tsbischof/kunst-und-krebs/doc/box/PXL_20230809_095317557.MP.jpg

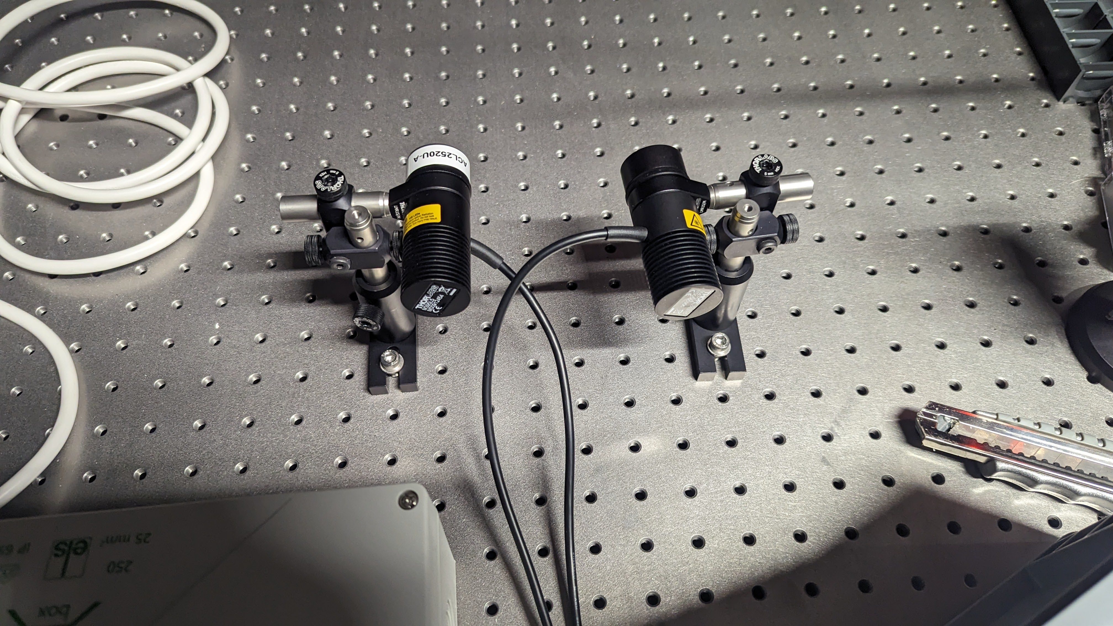
doc/box/PXL_20230809_095317557.MP.jpg
