tsbischof/kunst-und-krebs/doc/box/PXL_20230809_095553471.MP.jpg

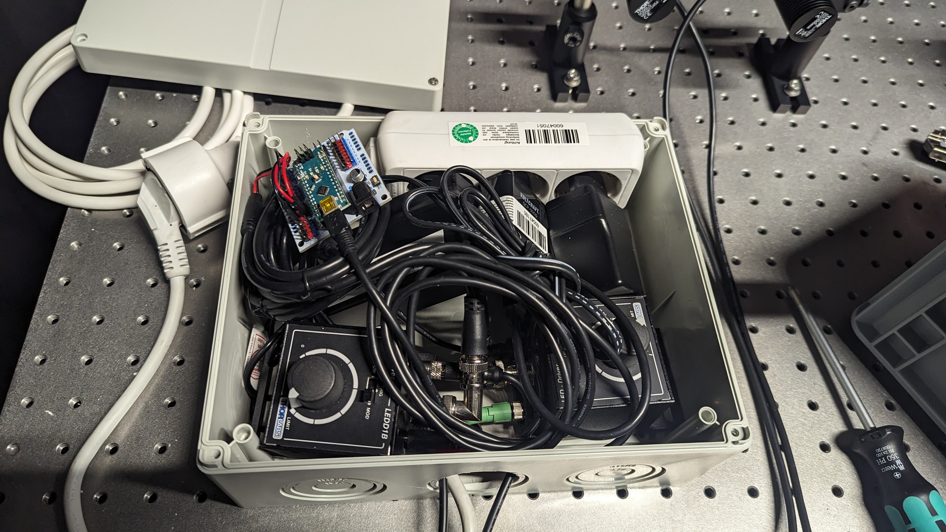
doc/box/PXL_20230809_095553471.MP.jpg
