tsbischof/kunst-und-krebs/doc/box/PXL_20230809_095557391.MP.jpg

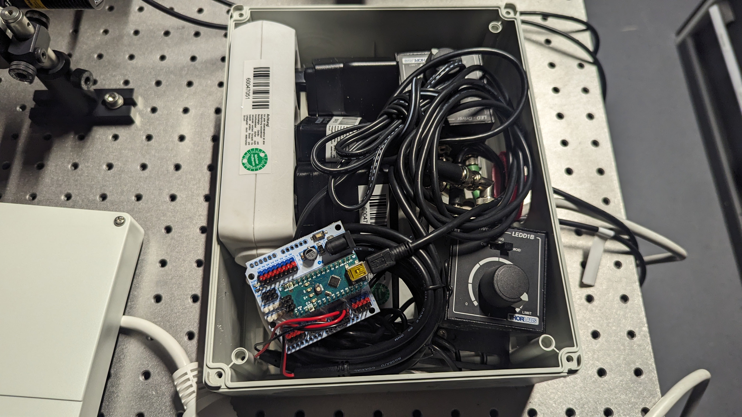
doc/box/PXL_20230809_095557391.MP.jpg
