tsbischof/kunst-und-krebs/doc/box/PXL_20230809_095600028.MP.jpg

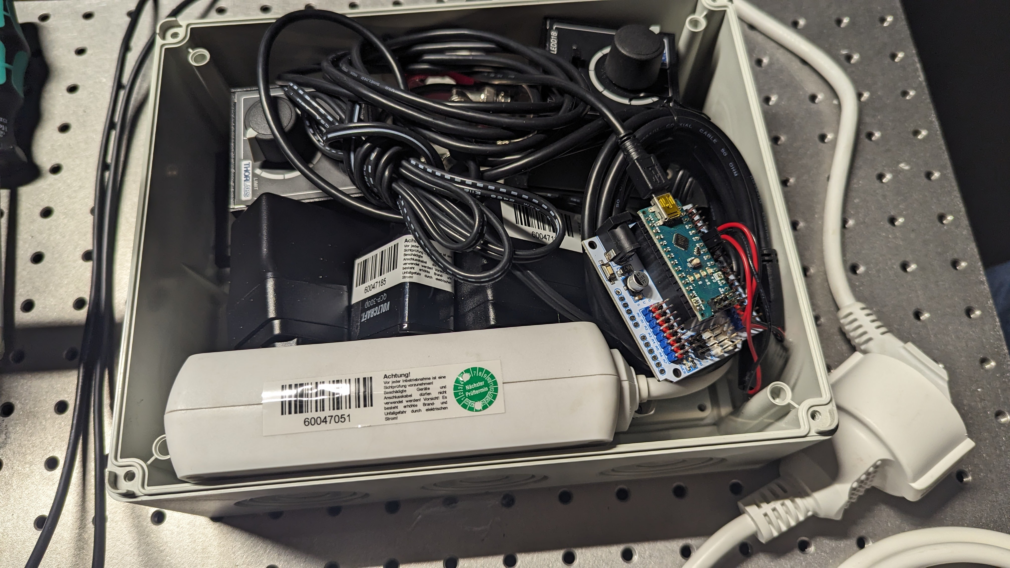
doc/box/PXL_20230809_095600028.MP.jpg
