tsbischof/kunst-und-krebs/doc/christians_technikshop/100381/Nano V3.0 Prototype Shield mehr Inputs und Outputs am Arduino Nano,_files/10-stueck-push-button-6-x-6mm-dip-tht-4-pin_002.jpg

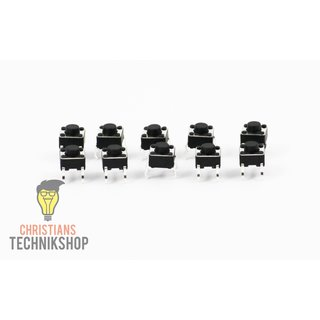
doc/christians_technikshop/100381/Nano V3.0 Prototype Shield mehr Inputs und Outputs am Arduino Nano,_files/10-stueck-push-button-6-x-6mm-dip-tht-4-pin_002.jpg
