tsbischof/kunst-und-krebs/doc/christians_technikshop/100381/Nano V3.0 Prototype Shield mehr Inputs und Outputs am Arduino Nano,_files/28byj-48-5v-stepper-motor-4-phase-5-wire-elektrischer-sc_002.jpg

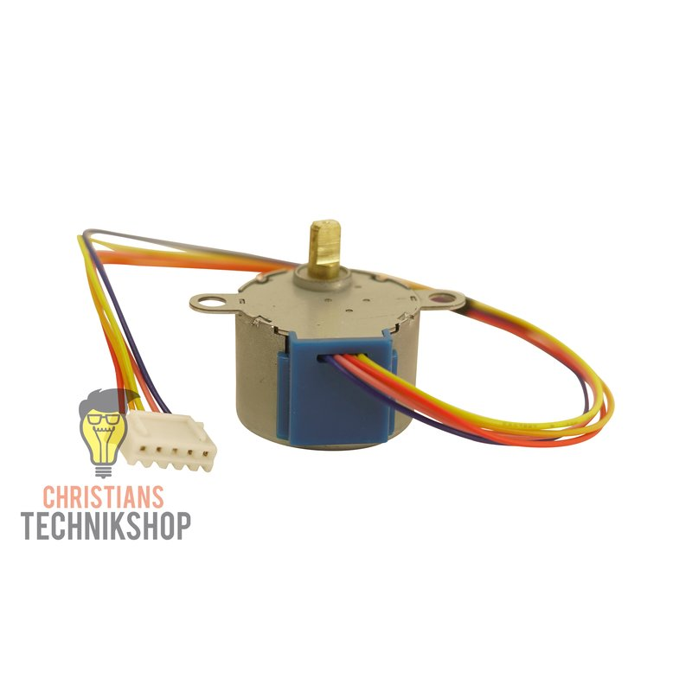
doc/christians_technikshop/100381/Nano V3.0 Prototype Shield mehr Inputs und Outputs am Arduino Nano,_files/28byj-48-5v-stepper-motor-4-phase-5-wire-elektrischer-sc_002.jpg
