tsbischof/kunst-und-krebs/doc/christians_technikshop/100381/Nano V3.0 Prototype Shield mehr Inputs und Outputs am Arduino Nano,_files/arduino-drehregler-drehgeber-rotary-encoder-push-button-_003.jpg

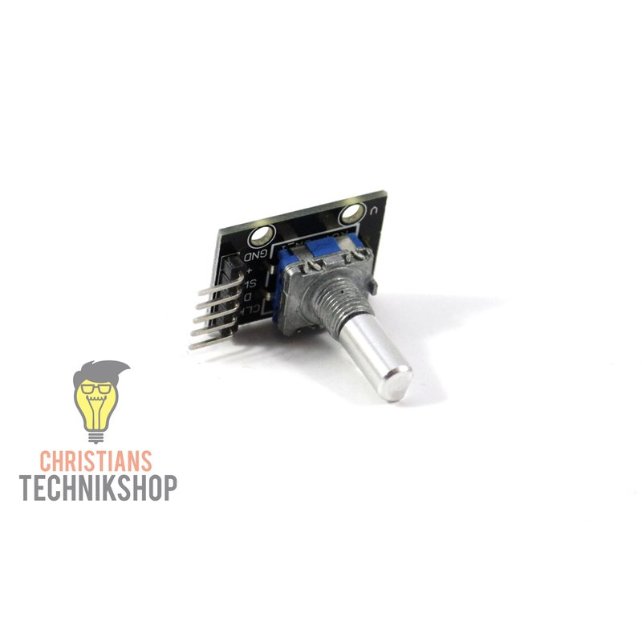
doc/christians_technikshop/100381/Nano V3.0 Prototype Shield mehr Inputs und Outputs am Arduino Nano,_files/arduino-drehregler-drehgeber-rotary-encoder-push-button-_003.jpg
