tsbischof/kunst-und-krebs/doc/christians_technikshop/100381/Nano V3.0 Prototype Shield mehr Inputs und Outputs am Arduino Nano,_files/nano-v3-entwicklerboard-fuer-arduino-ide-atmel-atmega328_003.jpg

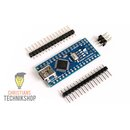
doc/christians_technikshop/100381/Nano V3.0 Prototype Shield mehr Inputs und Outputs am Arduino Nano,_files/nano-v3-entwicklerboard-fuer-arduino-ide-atmel-atmega328_003.jpg
