tsbischof/kunst-und-krebs/doc/christians_technikshop/100381/Nano V3.0 Prototype Shield mehr Inputs und Outputs am Arduino Nano,_files/nano-v30-prototype-shield-mehr-inputs-und-outputs-am-ard_004.jpg

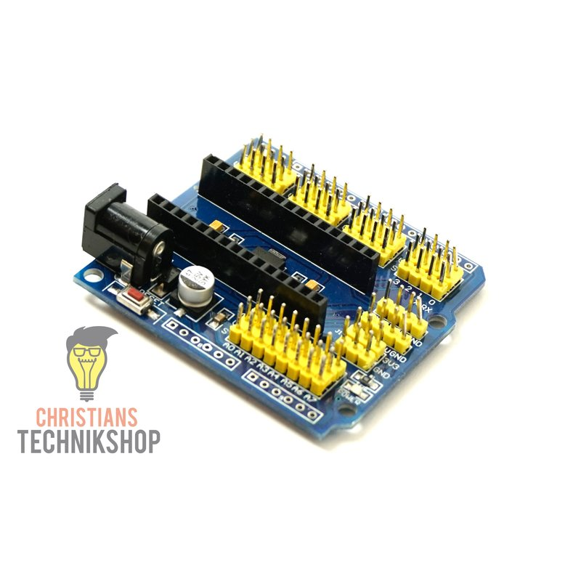
doc/christians_technikshop/100381/Nano V3.0 Prototype Shield mehr Inputs und Outputs am Arduino Nano,_files/nano-v30-prototype-shield-mehr-inputs-und-outputs-am-ard_004.jpg
