tsbischof/kunst-und-krebs/doc/christians_technikshop/100381/Nano V3.0 Prototype Shield mehr Inputs und Outputs am Arduino Nano,_files/plato-170-mikroschere-seitenschneider-fuer-draht-und-k_002.jpg

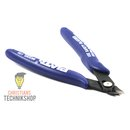
doc/christians_technikshop/100381/Nano V3.0 Prototype Shield mehr Inputs und Outputs am Arduino Nano,_files/plato-170-mikroschere-seitenschneider-fuer-draht-und-k_002.jpg
