tsbischof/kunst-und-krebs/doc/in_situ/PXL_20230809_135850603.MP.jpg

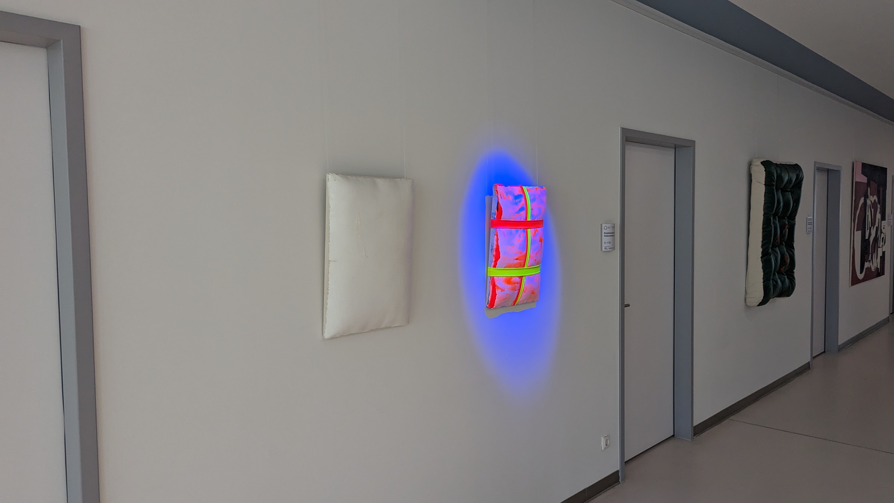
doc/in_situ/PXL_20230809_135850603.MP.jpg
