tsbischof/kunst-und-krebs/doc/in_situ/PXL_20230809_135857765.MP.jpg

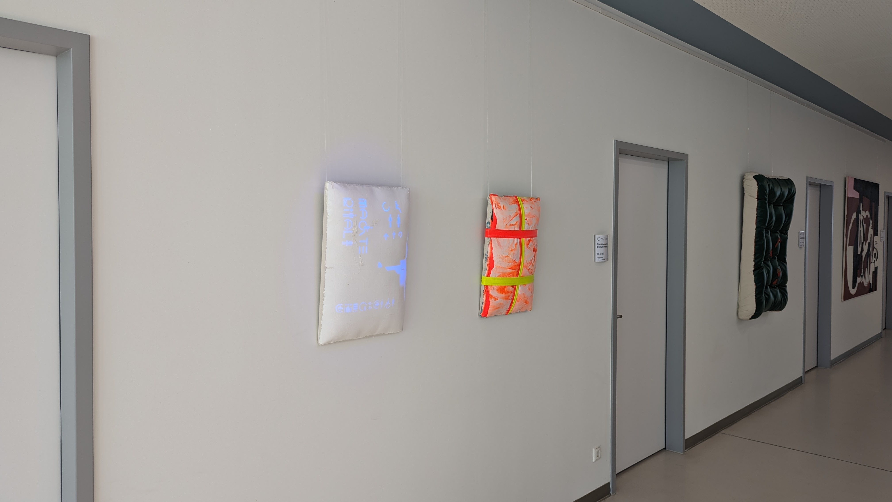
doc/in_situ/PXL_20230809_135857765.MP.jpg
