tsbischof/kunst-und-krebs/doc/in_situ/PXL_20230809_141232840.MP.jpg

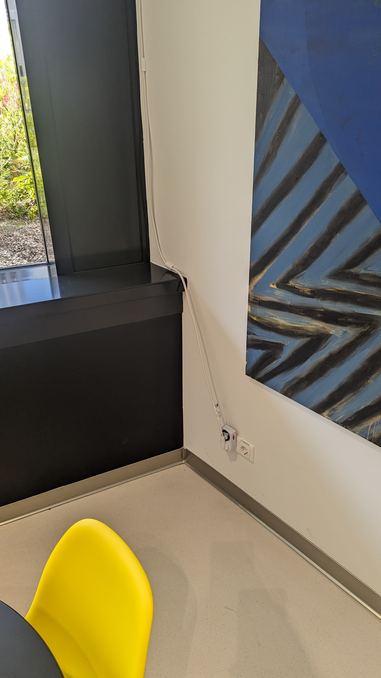
doc/in_situ/PXL_20230809_141232840.MP.jpg
