tsbischof/kunst-und-krebs/doc/in_situ/PXL_20230809_141235253.MP.jpg

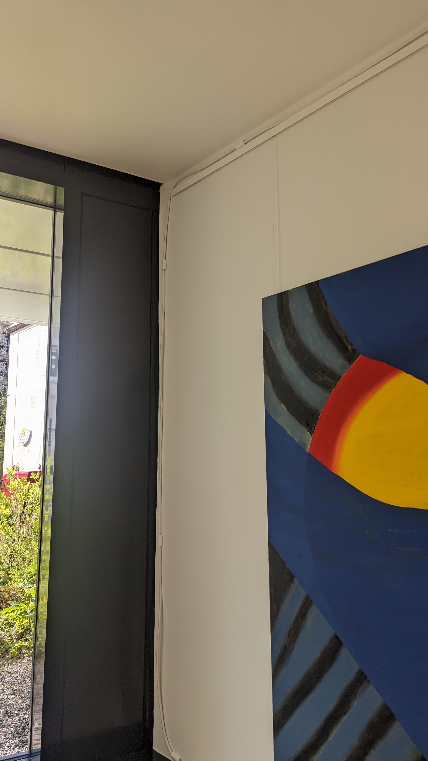
doc/in_situ/PXL_20230809_141235253.MP.jpg
