tsbischof/kunst-und-krebs/doc/in_situ/PXL_20230809_141242949.MP.jpg

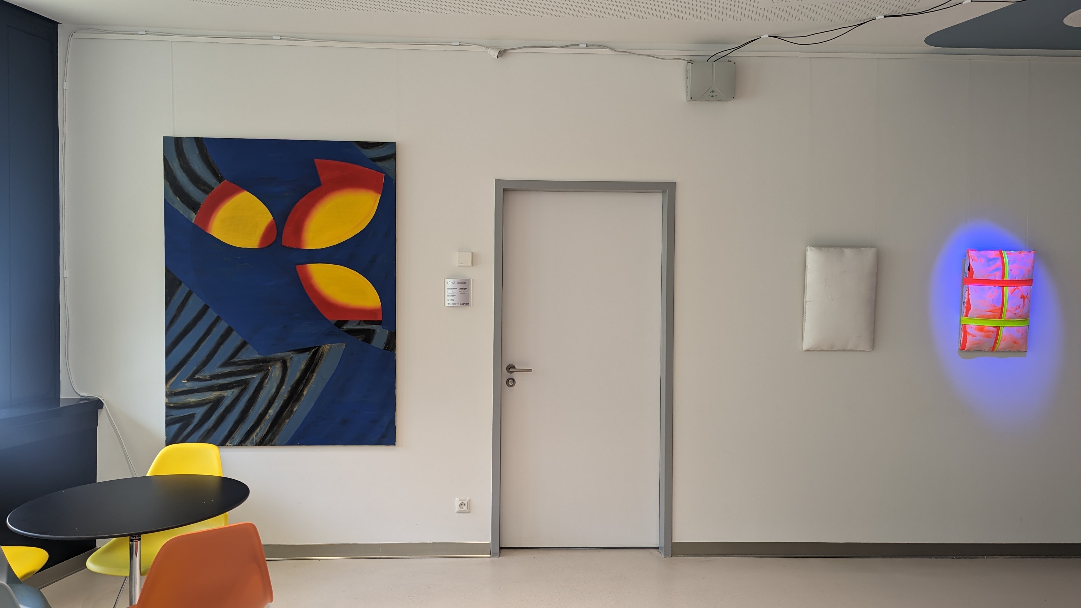
doc/in_situ/PXL_20230809_141242949.MP.jpg
