tsbischof/kunst-und-krebs/doc/in_situ/PXL_20230809_141327290.MP.jpg

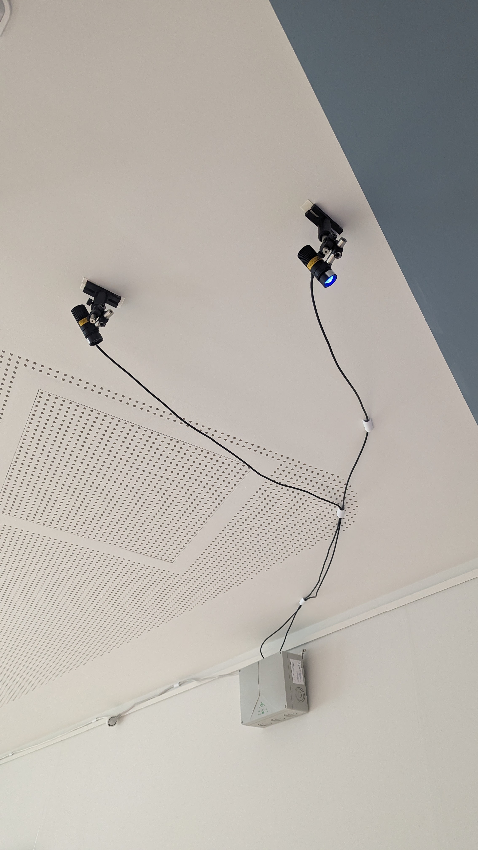
doc/in_situ/PXL_20230809_141327290.MP.jpg
