tsbischof/kunst-und-krebs/doc/in_situ/PXL_20230925_123240814.MP.jpg

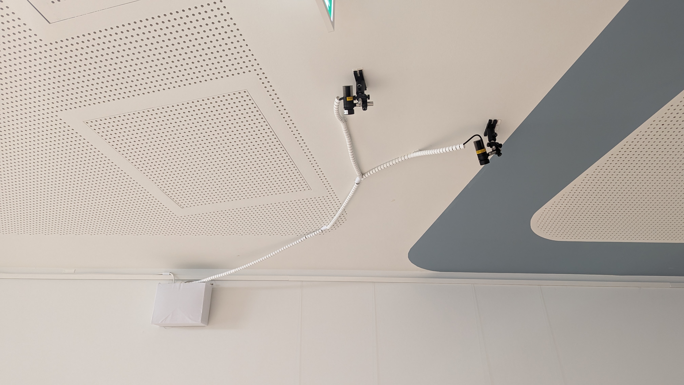
doc/in_situ/PXL_20230925_123240814.MP.jpg
