tsbischof/kunst-und-krebs/doc/spelsberg/82591001/82591001_M-490-925-01_V1.jpg

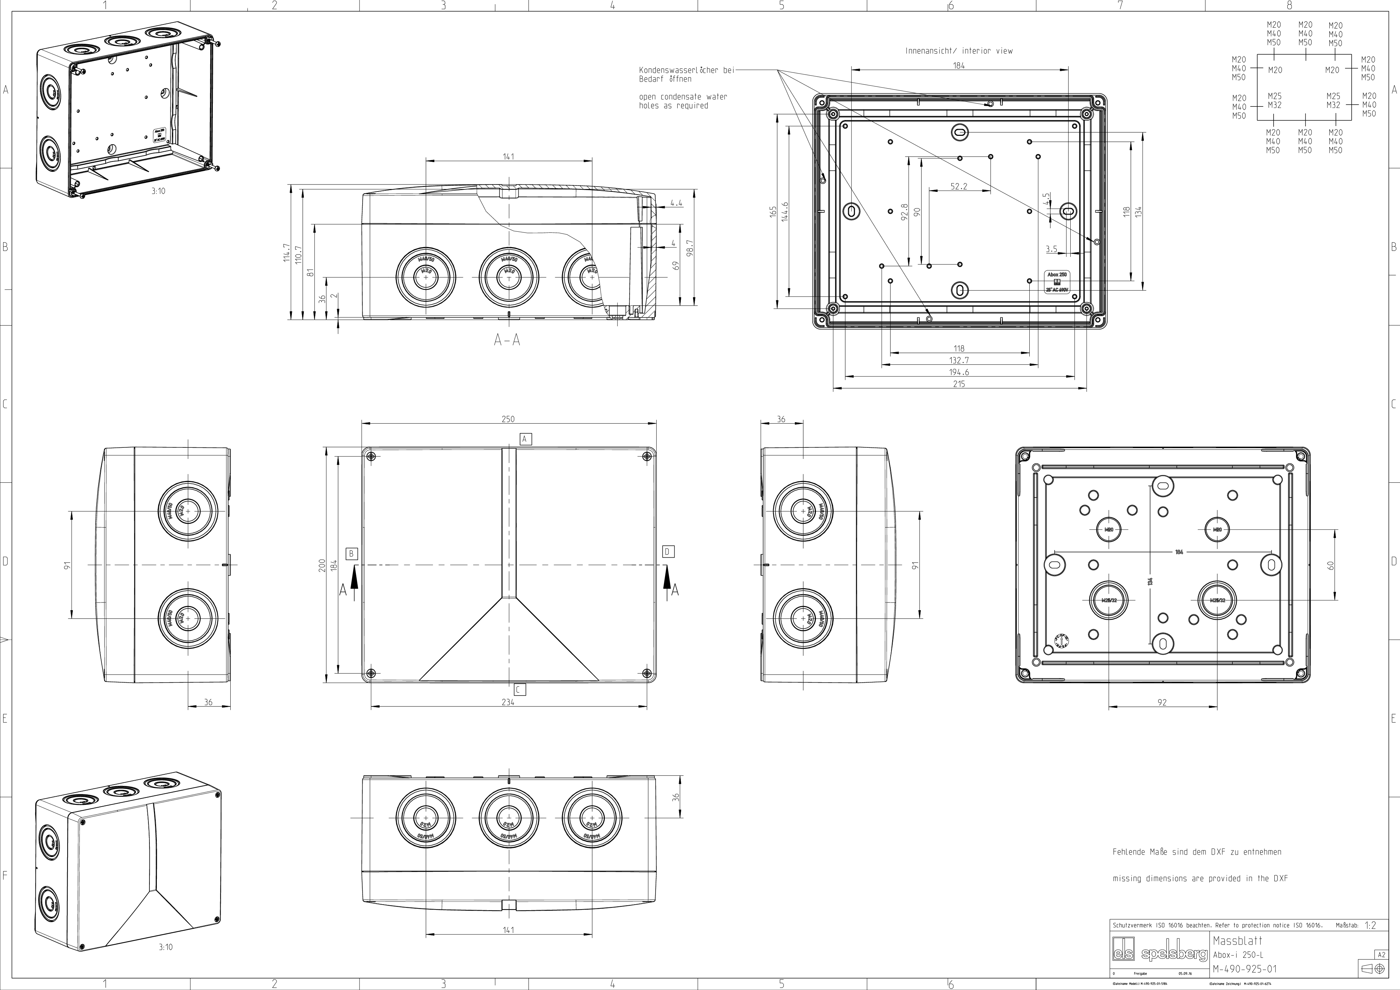
doc/spelsberg/82591001/82591001_M-490-925-01_V1.jpg
