tsbischof/kunst-und-krebs/doc/thorlabs/BA1M/BA1_M-AutoCADDXF.dxf

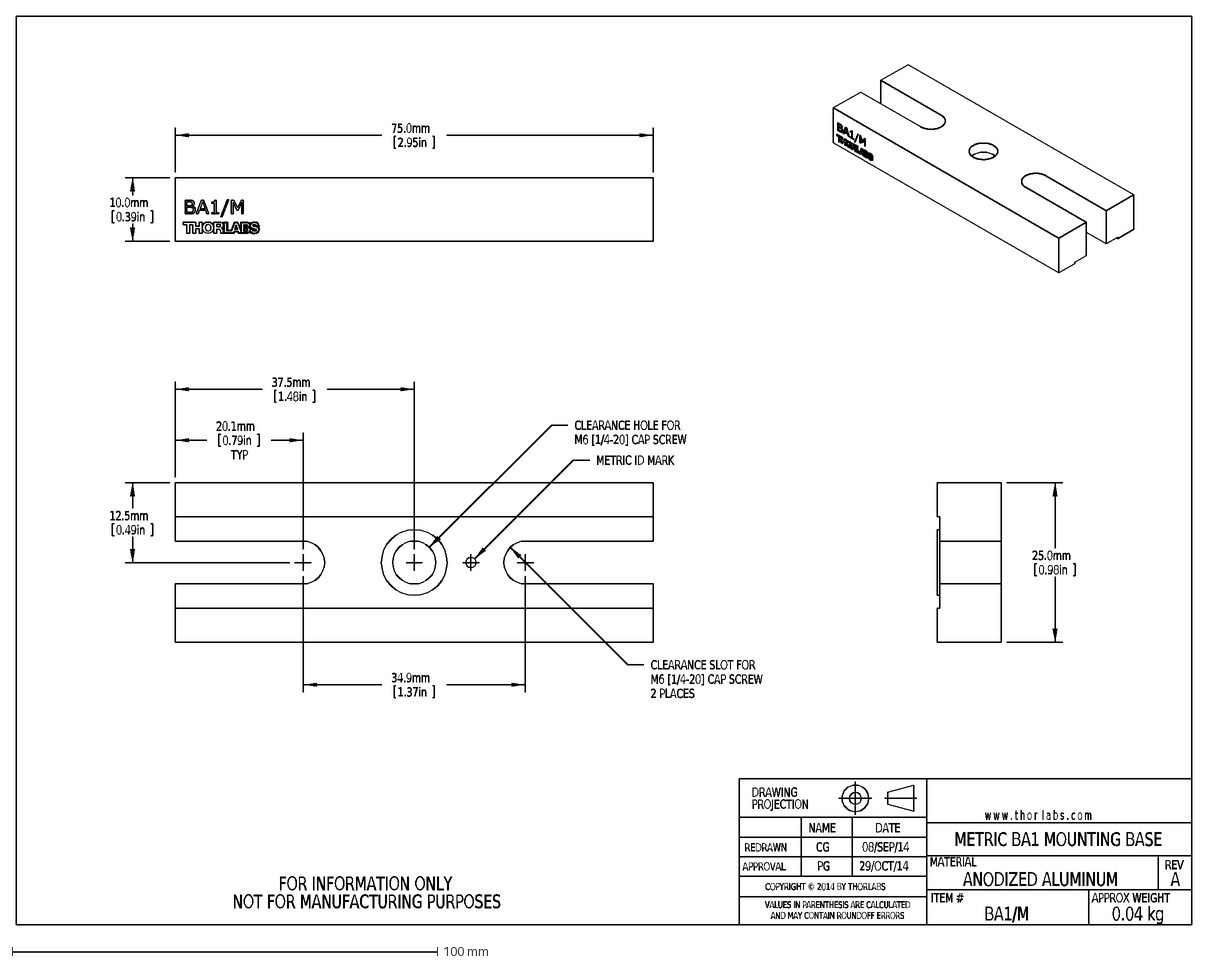
[picture p44: CAD file, 2023-08-09]
doc/thorlabs/BA1M/BA1_M-AutoCADDXF.dxf
A
BA1/M
MATERIAL
REDRAWN
APPROVAL
REV
CG
PG
08/SEP/14
DATE
29/OCT/14
w w w . t h o r l a b s . c o m
ITEM #
APPROX WEIGHT
ANODIZED ALUMINUM
0.04 kg
VALUES IN PARENTHESIS ARE CALCULATED
AND MAY CONTAIN ROUNDOFF ERRORS
DRAWING
PROJECTION
NAME
FOR INFORMATION ONLY
NOT FOR MANUFACTURING PURPOSES
METRIC BA1 MOUNTING BASE
COPYRIGHT © 2014 BY THORLABS
12.5mm
0.49in
20.1mm
TYP
0.79in
37.5mm
1.48in
34.9mm
1.37in
M6 [1/4-20] CAP SCREW
CLEARANCE HOLE FOR
2 PLACES
CLEARANCE SLOT FOR
METRIC ID MARK
75.0mm
2.95in
10.0mm
0.39in
25.0mm
0.98in
