tsbischof/kunst-und-krebs/doc/thorlabs/KPS201/KPS201-Solidworks.sldprt

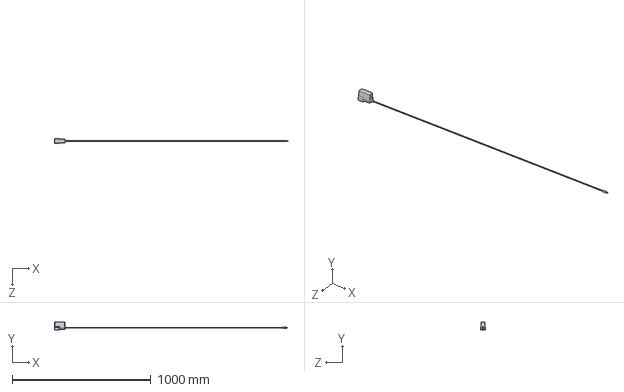
[picture p45: CAD file, 2023-08-09]
doc/thorlabs/KPS201/KPS201-Solidworks.sldprt
1680.5 x 57.0 x 39.1 mm
