tsbischof/kunst-und-krebs/doc/thorlabs/LEDD1B/LEDD1B-Solidworks.sldprt

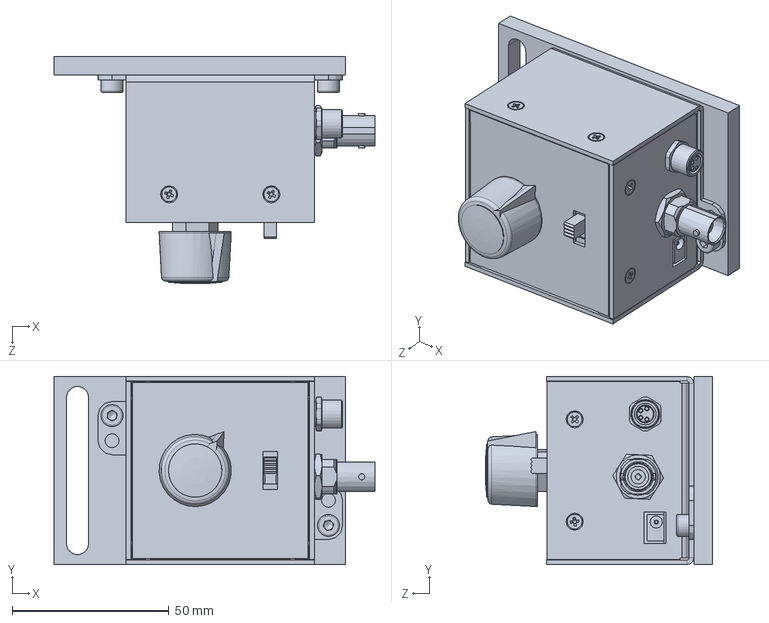
[picture p46: CAD file, 2023-08-09]
doc/thorlabs/LEDD1B/LEDD1B-Solidworks.sldprt
102.3 x 60.0 x 72.5 mm
