tsbischof/kunst-und-krebs/doc/thorlabs/BA1M/BA1_M-AutoCADPDF.pdf

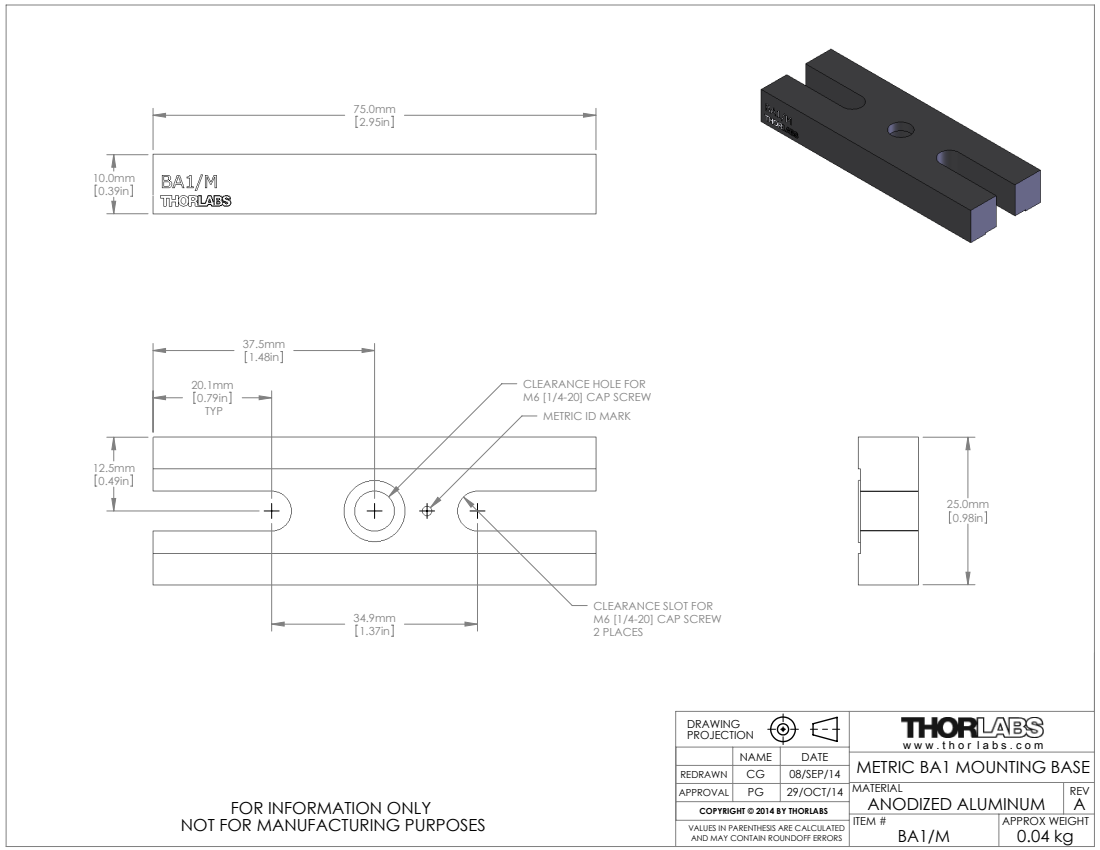
[picture p47: page 1]
ITEM #; APPROX WEIGHT

CLEARANCE HOLE FOR
M6 [1/4-20] CAP SCREW
METRIC ID MARK

CLEARANCE SLOT FOR
2 PLACES

DRAWING PROJECTION | | w w w . t h o r l a b s . c o m

NAME | DATE
APPROVAL | PG | 29/OCT/14 | MATERIAL ANODIZED ALUMINUM | REV A

METRIC BA1 MOUNTING BASE

REDRAWN | CG | 08/SEP/14

FOR INFORMATION ONLY
NOT FOR MANUFACTURING PURPOSES

COPYRIGHT © 2014 BY THORLABS
0.04 kg VALUES IN PARENTHESIS ARE CALCULATED
AND MAY CONTAIN ROUNDOFF ERRORS
