tsbischof/kunst-und-krebs/doc/thorlabs/M395L5/M395L5-AutoCADPDF.pdf

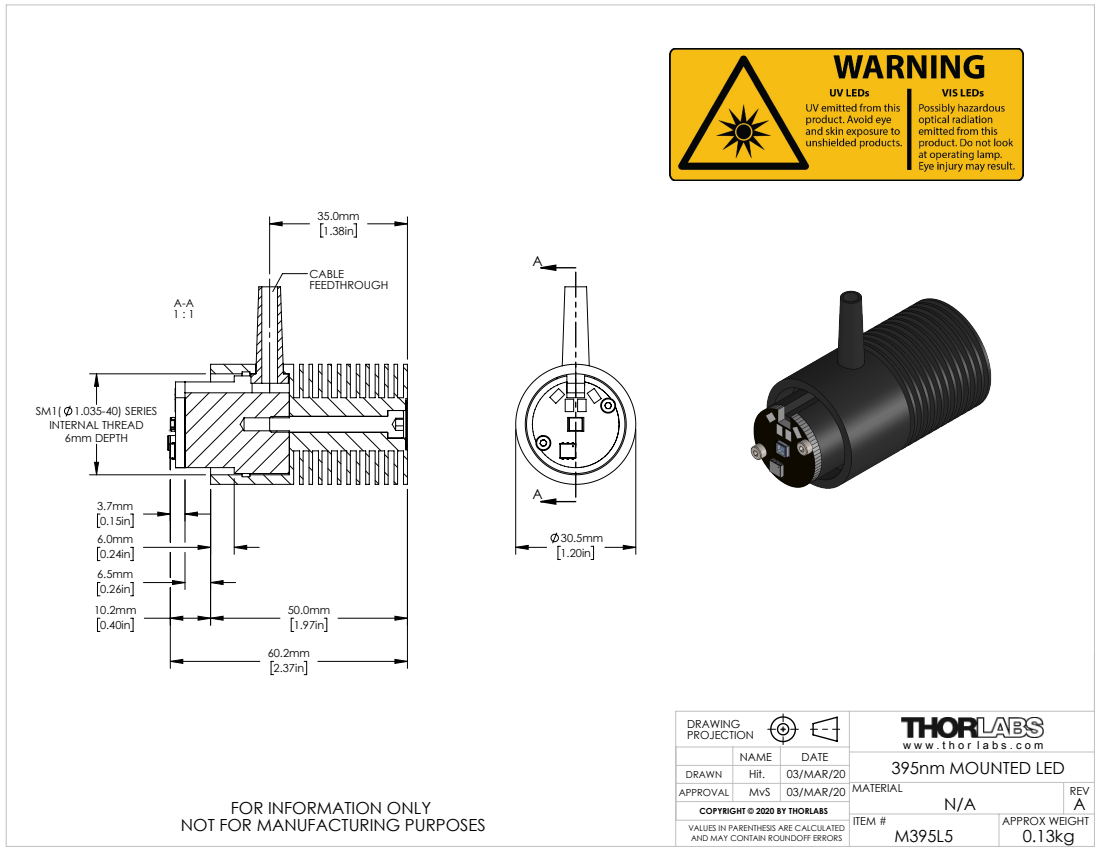
[picture p48: page 1]
SM1( 1.035-40) SERIES INTERNAL THREAD 6mm DEPTH; ITEM #; APPROX WEIGHT; 395nm MOUNTED LED

DRAWING PROJECTION | | w w w . t h o r l a b s . c o m

NAME | DATE
APPROVAL | MvS | 03/MAR/20 | MATERIAL N/A | REV A

DRAWN | Hit. | 03/MAR/20

FOR INFORMATION ONLY
NOT FOR MANUFACTURING PURPOSES

COPYRIGHT © 2020 BY THORLABS
0.13kg VALUES IN PARENTHESIS ARE CALCULATED
AND MAY CONTAIN ROUNDOFF ERRORS
