tsbischof/kunst-und-krebs/doc/thorlabs/M470L4/M470L4-AutoCADPDF.pdf

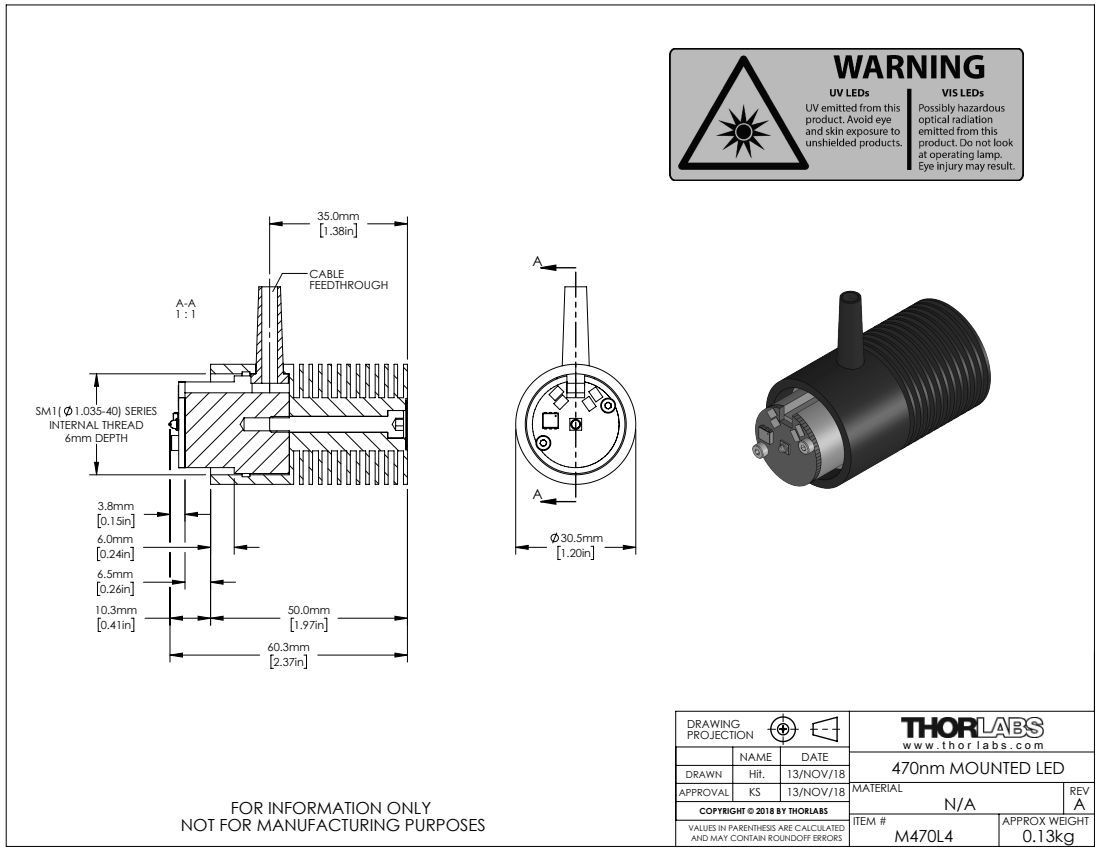
[picture p49: page 1]
SM1( 1.035-40) SERIES INTERNAL THREAD 6mm DEPTH; ITEM #; APPROX WEIGHT; 470nm MOUNTED LED

DRAWING PROJECTION | | w w w . t h o r l a b s . c o m

NAME | DATE
APPROVAL | KS | 13/NOV/18 | MATERIAL N/A | REV A

DRAWN | Hit. | 13/NOV/18

FOR INFORMATION ONLY
NOT FOR MANUFACTURING PURPOSES

COPYRIGHT © 2018 BY THORLABS
0.13kg VALUES IN PARENTHESIS ARE CALCULATED
AND MAY CONTAIN ROUNDOFF ERRORS
