tsbischof/kunst-und-krebs/doc/thorlabs/PH50M/PH50_M-AutoCADPDF.pdf

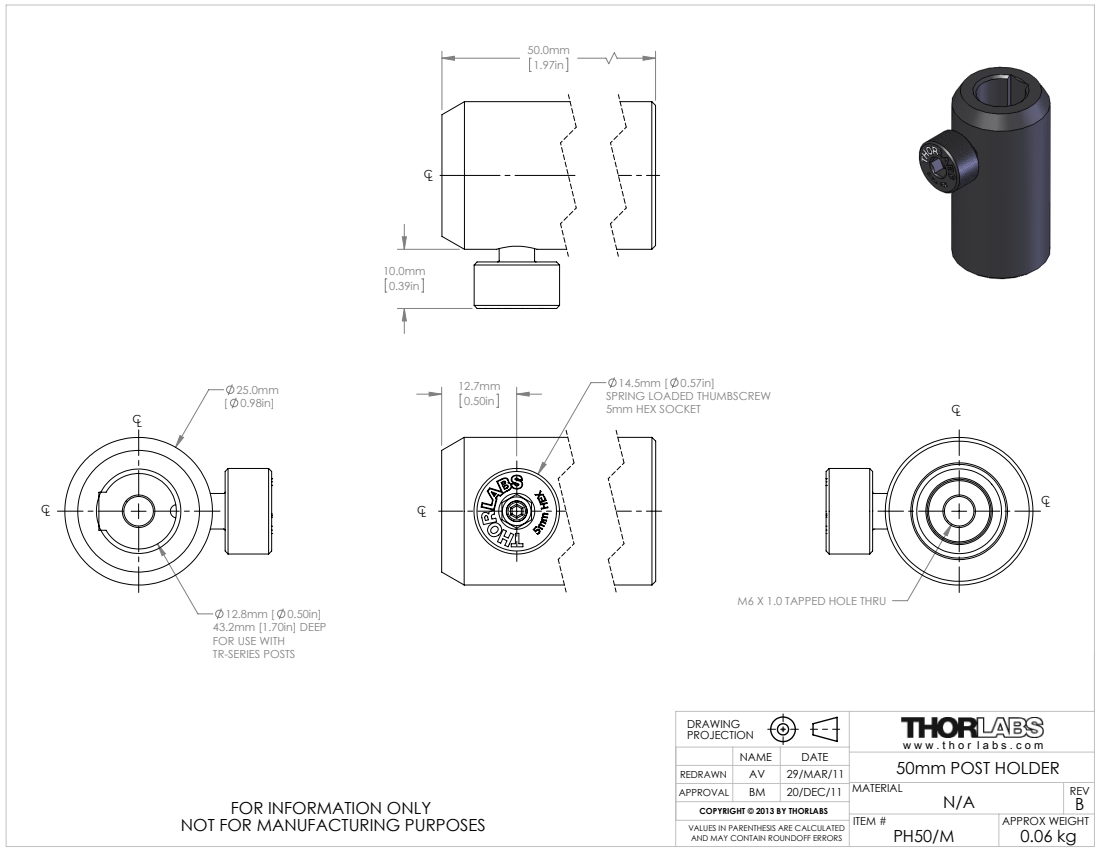
[picture p50: page 1]
ITEM #; APPROX WEIGHT; 50mm POST HOLDER

SPRING LOADED THUMBSCREW
5mm HEX SOCKET

M6 X 1.0 TAPPED HOLE THRU

43.2mm [1.70in] DEEP
FOR USE WITH
TR-SERIES POSTS

DRAWING PROJECTION | | w w w . t h o r l a b s . c o m

NAME | DATE
APPROVAL | BM | 20/DEC/11 | MATERIAL N/A | REV B

REDRAWN | AV | 29/MAR/11

FOR INFORMATION ONLY
NOT FOR MANUFACTURING PURPOSES

COPYRIGHT © 2013 BY THORLABS
0.06 kg VALUES IN PARENTHESIS ARE CALCULATED
AND MAY CONTAIN ROUNDOFF ERRORS
