tsbischof/kunst-und-krebs/breathe/breath.h

#define BREATH {0,0,0,0,0,0,0,0,0,0,0,0,0,0,0,0,0,0,0,0,0,0,0,0,0,0,0,0,0,0,0,0,0,0,0,0,0,0,0,0,0,0,0,0,0,0,0,0,0,0,0,0,0,0,0,0,0,0,0,0,0,0,0,0,0,0,0,0,0,0,0,0,0,0,0,0,0,0,0,0,0,0,0,0,0,0,0,0,0,0,0,0,0,0,0,0,0,0,0,0,0,0,0,0,0,0,0,0,0,0,0,0,0,0,0,0,0,0,0,0,0,0,0,0,0,0,0,0,0,0,0,0,0,0,0,0,0,0,0,0,0,0,0,0,0,0,0,0,0,0,0,0,0,0,1,1,1,1,1,1,1,1,1,1,1,1,1,1,1,1,1,1,1,2,2,2,2,2,2,2,2,2,2,2,2,3,3,3,3,3,3,3,3,3,3,4,4,4,4,4,4,4,5,5,5,5,5,5,6,6,6,6,6,6,7,7,7,7,7,8,8,8,8,9,9,9,9,10,10,10,10,11,11,11,11,12,12,12,13,13,13,14,14,14,15,15,15,16,16,17,17,17,18,18,19,19,19,20,20,21,21,22,22,23,23,24,24,25,25,26,26,27,27,28,29,29,30,30,31,31,32,33,33,34,35,35,36,37,37,38,39,39,40,41,42,42,43,44,45,45,46,47,48,49,50,50,51,52,53,54,55,56,57,57,58,59,60,61,62,63,64,65,66,67,68,69,70,71,72,73,74,75,76,77,78,80,81,82,83,84,85,86,87,89,90,91,92,93,94,96,97,98,99,100,102,103,104,105,107,108,109,110,112,113,114,116,117,118,119,121,122,123,125,126,127,129,130,131,133,134,135,137,138,139,141,142,143,145,146,147,149,150,151,153,154,155,157,158,159,161,162,163,165,166,167,169,170,171,173,174,175,177,178,179,181,182,183,184,186,187,188,189,191,192,193,194,196,197,198,199,201,202,203,204,205,206,207,209,210,211,212,213,214,215,216,217,218,219,220,221,222,223,224,225,226,227,228,229,230,231,232,233,233,234,235,236,237,237,238,239,240,240,241,242,242,243,243,244,245,245,246,246,247,247,248,248,249,249,250,250,250,251,251,252,252,252,252,253,253,253,253,254,254,254,254,254,254,254,254,254,254,255,254,254,254,254,254,254,254,254,254,254,253,253,253,253,252,252,252,252,251,251,250,250,250,249,249,248,248,247,247,246,246,245,245,244,243,243,242,242,241,240,240,239,238,237,237,236,235,234,233,233,232,231,230,229,228,227,226,225,224,223,222,221,220,219,218,217,216,215,214,213,212,211,210,209,207,206,205,204,203,202,201,199,198,197,196,194,193,192,191,189,188,187,186,184,183,182,181,179,178,177,175,174,173,171,170,169,167,166,165,163,162,161,159,158,157,155,154,153,151,150,149,147,146,145,143,142,141,139,138,137,135,134,133,131,130,129,127,126,125,123,122,121,119,118,117,116,114,113,112,110,109,108,107,105,104,103,102,100,99,98,97,96,94,93,92,91,90,89,87,86,85,84,83,82,81,80,78,77,76,75,74,73,72,71,70,69,68,67,66,65,64,63,62,61,60,59,58,57,57,56,55,54,53,52,51,50,50,49,48,47,46,45,45,44,43,42,42,41,40,39,39,38,37,37,36,35,35,34,33,33,32,31,31,30,30,29,29,28,27,27,26,26,25,25,24,24,23,23,22,22,21,21,20,20,19,19,19,18,18,17,17,17,16,16,15,15,15,14,14,14,13,13,13,12,12,12,11,11,11,11,10,10,10,10,9,9,9,9,8,8,8,8,7,7,7,7,7,6,6,6,6,6,6,5,5,5,5,5,5,4,4,4,4,4,4,4,3,3,3,3,3,3,3,3,3,3,2,2,2,2,2,2,2,2,2,2,2,2,1,1,1,1,1,1,1,1,1,1,1,1,1,1,1,1,1,1,1,0,0,0,0,0,0,0,0,0,0,0,0,0,0,0,0,0,0,0,0,0,0,0,0,0,0,0,0,0,0,0,0,0,0,0,0,0,0,0,0,0,0,0,0,0,0,0,0,0,0,0,0,0,0,0,0,0,0,0,0,0,0,0,0,0,0,0,0,0,0,0,0,0,0,0,0,0,0,0,0,0,0,0,0,0,0,0,0,0,0,0,0,0,0,0,0,0,0,0,0,0,0,0,0,0,0,0,0,0,0,0,0,0,0,0,0,0,0,0,0,0,0,0,0,0,0,0,0,0,0,0,0,0,0,0,0,0,0,0,0,0,0,0,0,0,0,0,0,0,0,0,0,0,0}
